GJN-Aerospace/CanSat2020/Ground Station/Hardware/Antenna/Balun.png

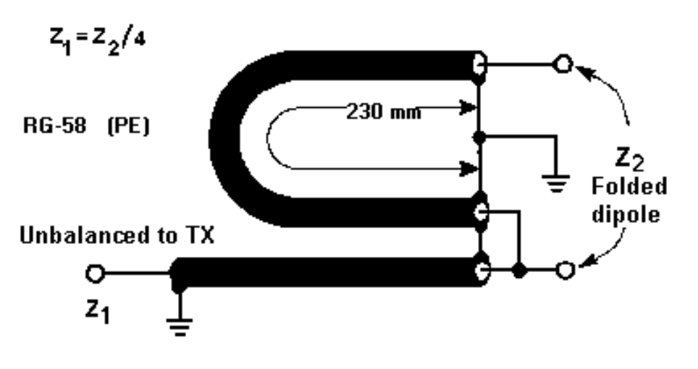
Ground Station/Hardware/Antenna/Balun.png
