GJN-Aerospace/CanSat2020/Probe/Hardware/Components/Battery/Nabíječka Li-ion článku TP4056 s ochranou/LA120013-1.png

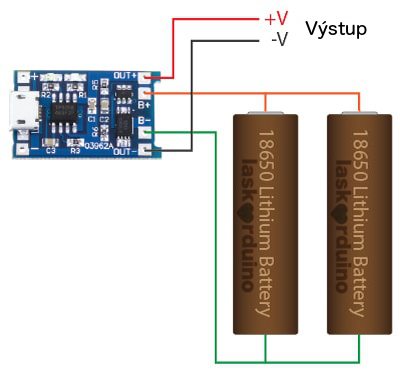
Probe/Hardware/Components/Battery/Nabíječka Li-ion článku TP4056 s ochranou/LA120013-1.png
