GJN-Aerospace/CanSat2020/Probe/Hardware/Components/Battery/Nabíječka Li-ion článku TP4056 s ochranou/TP4056_Protected_Battery_Charger-3.png

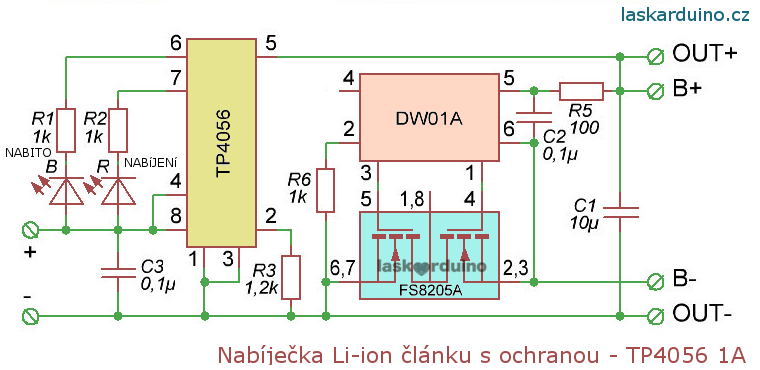
Probe/Hardware/Components/Battery/Nabíječka Li-ion článku TP4056 s ochranou/TP4056_Protected_Battery_Charger-3.png
