GJN-Aerospace/CanSat2020/Probe/Hardware/Components/BME280/Screenshot 2020-01-01 at 14.22.14.png

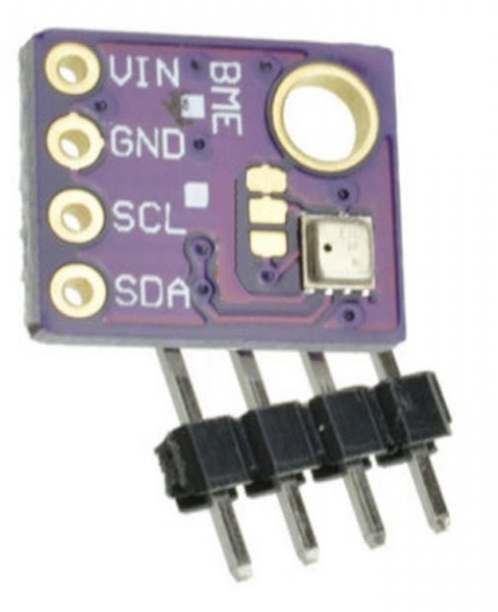
Probe/Hardware/Components/BME280/Screenshot 2020-01-01 at 14.22.14.png
