GJN-Aerospace/CanSat2020/Probe/Hardware/Components/Development board Ncleo F411RE/mbed.com/nucleo_f411re_2017_11_14_ard_left.png

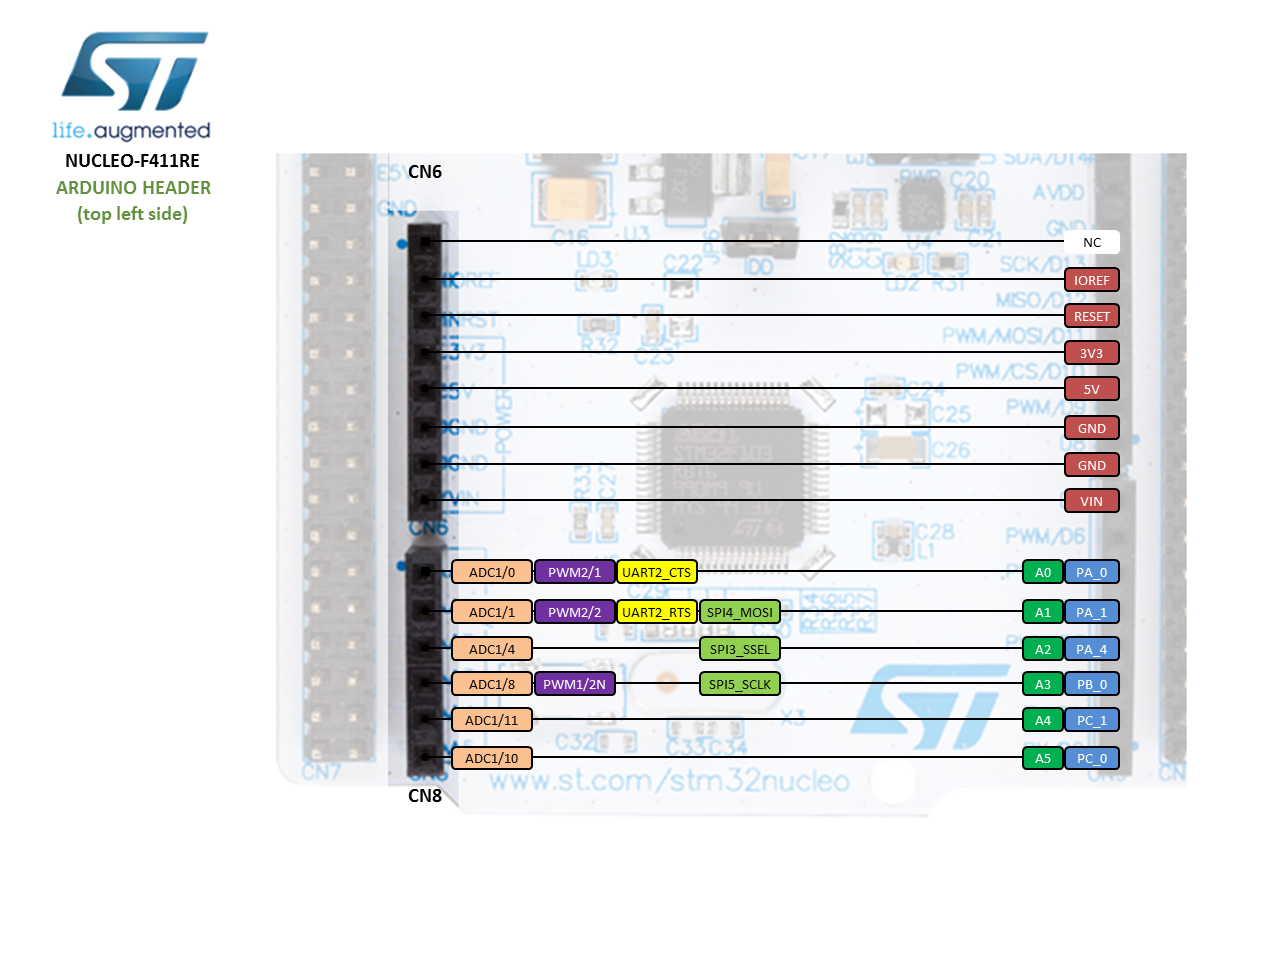
Probe/Hardware/Components/Development board Ncleo F411RE/mbed.com/nucleo_f411re_2017_11_14_ard_left.png
