GJN-Aerospace/CanSat2020/Probe/Hardware/Components/MicroSD Slot/GCT/Screenshot 2019-11-09 at 16.13.04.png

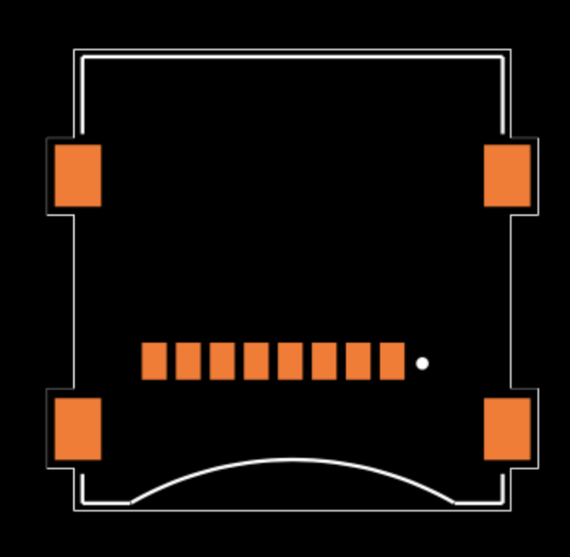
Probe/Hardware/Components/MicroSD Slot/GCT/Screenshot 2019-11-09 at 16.13.04.png
