GJN-Aerospace/CanSat2020/Probe/Hardware/Components/MPU-9250/Screenshot 2020-01-01 at 14.21.57.png

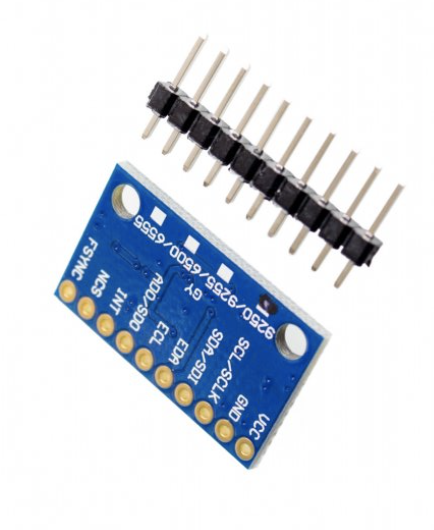
Probe/Hardware/Components/MPU-9250/Screenshot 2020-01-01 at 14.21.57.png
