GJN-Aerospace/CanSat2020/Probe/Hardware/Components/Programmer/STLink/Screenshot 2020-03-07 at 09.58.13.png

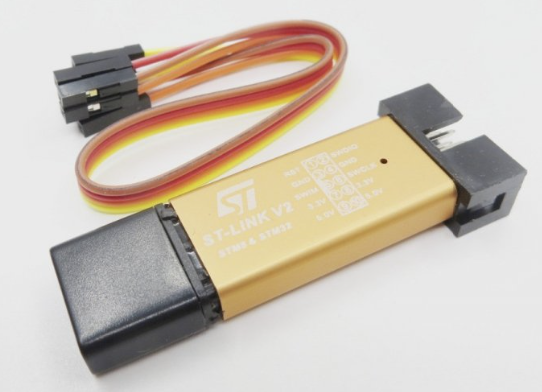
Probe/Hardware/Components/Programmer/STLink/Screenshot 2020-03-07 at 09.58.13.png
