GJN-Aerospace/CanSat2020/Probe/Hardware/Components/Programmer/UART/Screenshot 2020-03-07 at 09.57.16.png

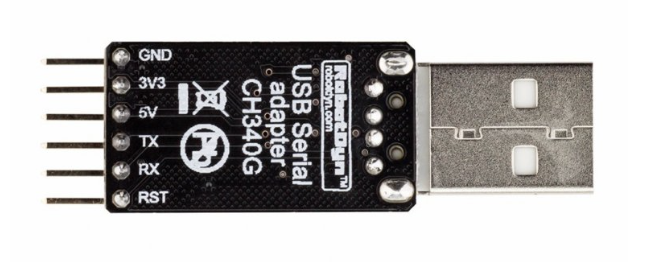
Probe/Hardware/Components/Programmer/UART/Screenshot 2020-03-07 at 09.57.16.png
