GJN-Aerospace/CanSat2020/Probe/openCanSat PKII/PouzdroOCS(PETG).stl

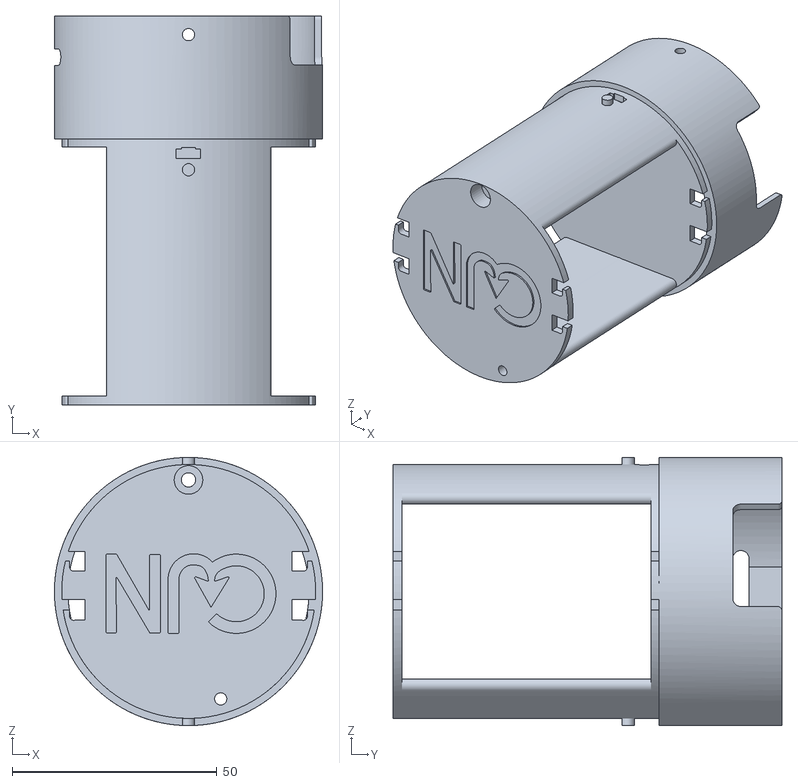
[picture p37: CAD file, 2020-08-19]
Probe/openCanSat PKII/PouzdroOCS(PETG).stl
65.5 x 95.0 x 65.5
