GJN-Aerospace/CanSat2020/Parachute/ParachuteRetainer.stl

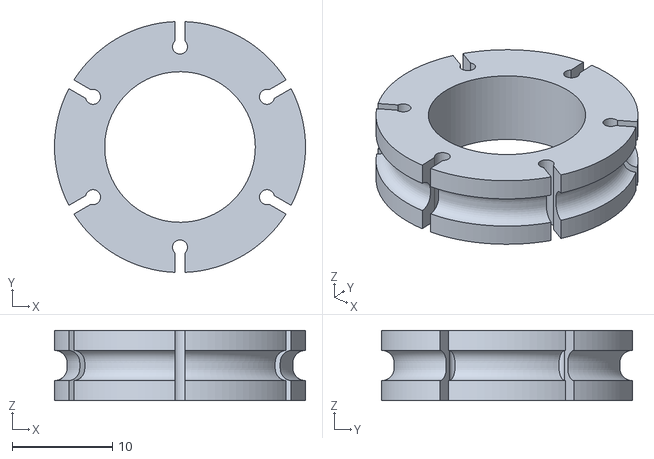
[picture p38: CAD file, 2020-08-19]
Parachute/ParachuteRetainer.stl
25.0 x 25.0 x 7.00
