GJN-Aerospace/CanSat2020/Probe/Hardware/Case/PlastPKII(TPU).stl

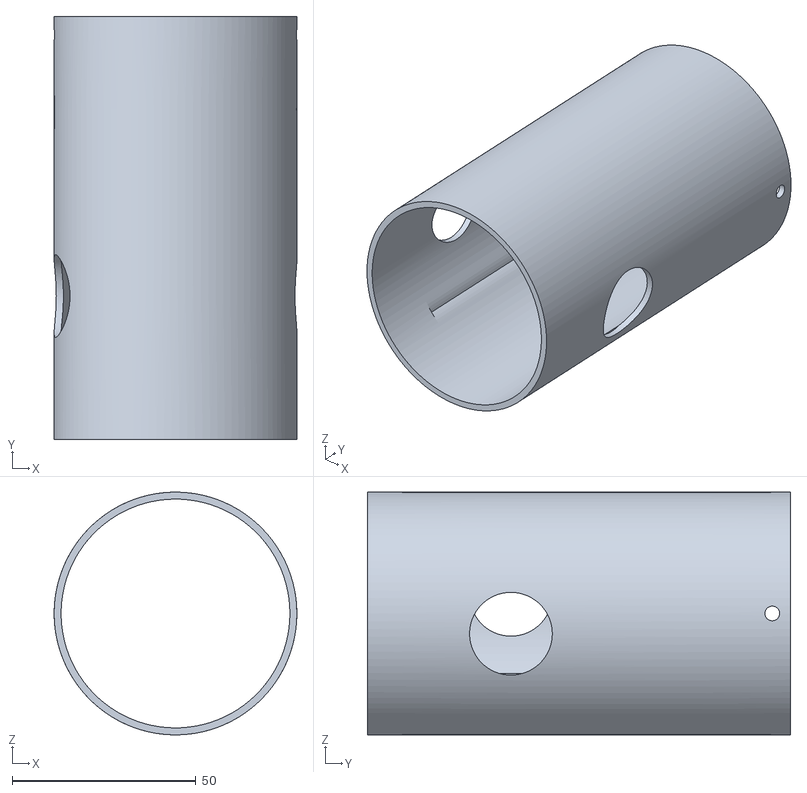
[picture p39: CAD file, 2020-08-19]
Probe/Hardware/Case/PlastPKII(TPU).stl
66.0 x 115.0 x 66.0
