GJN-Aerospace/CanSat2020/Parachute/Kolicek(6x, CPE, co nejdetailnejsi).stl

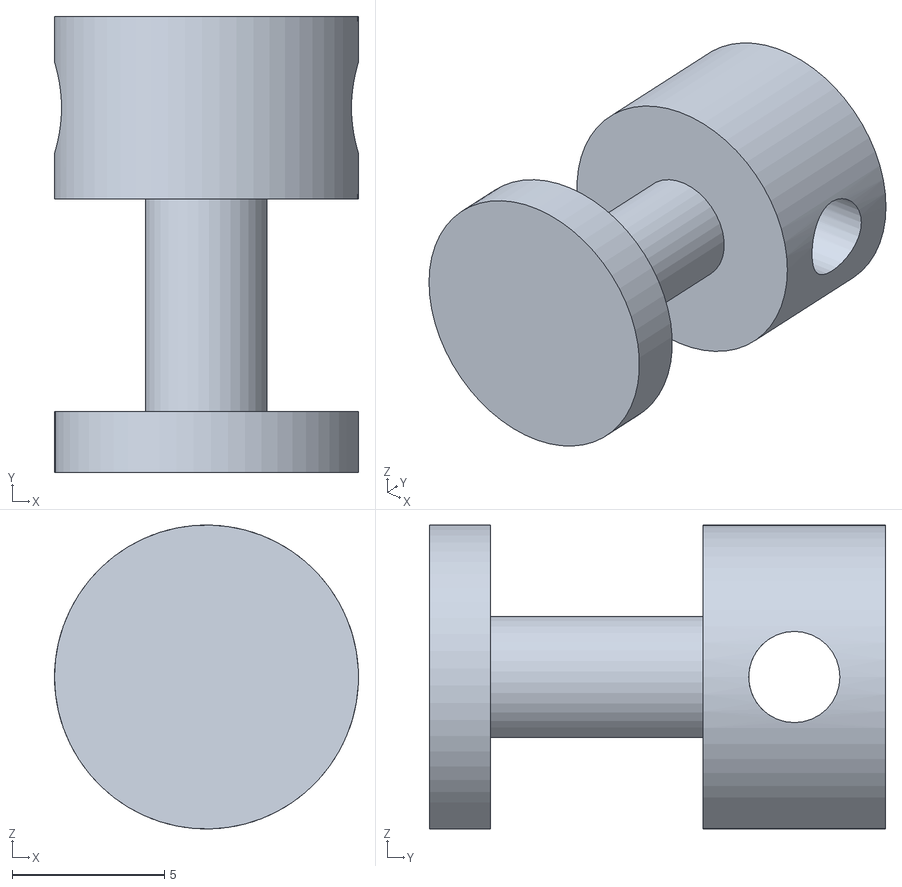
[picture p40: CAD file, 2020-08-19]
Parachute/Kolicek(6x, CPE, co nejdetailnejsi).stl
10.0 x 15.0 x 10.00
