GJN-Aerospace/CanSat2020/Probe/Hardware/Components/Connectors/Battery Connectors/PFH02-03P/dsh.800-085.1.pdf

2510型连接器承认图面 | E

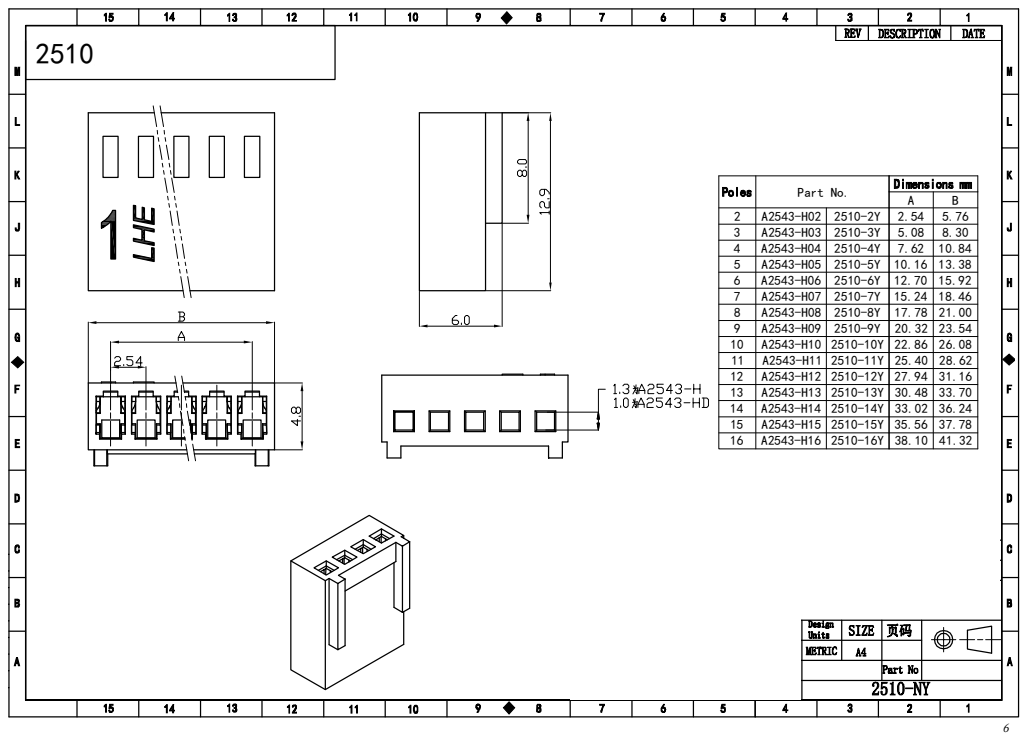
[picture p42: page 1]
PA66(UL94V-0) Housing; White（白色）; 浙江联和电子有限公司 ®; Part No.

27.94 31.16
30.48 33.70
33.02 36.24

ZHEJIANG LIANHE ELECTRONICS CO.,LTD
