GJN-Aerospace/CanSat2020/Probe/Hardware/Components/MicroSD Slot/dsh.832-271.1.pdf

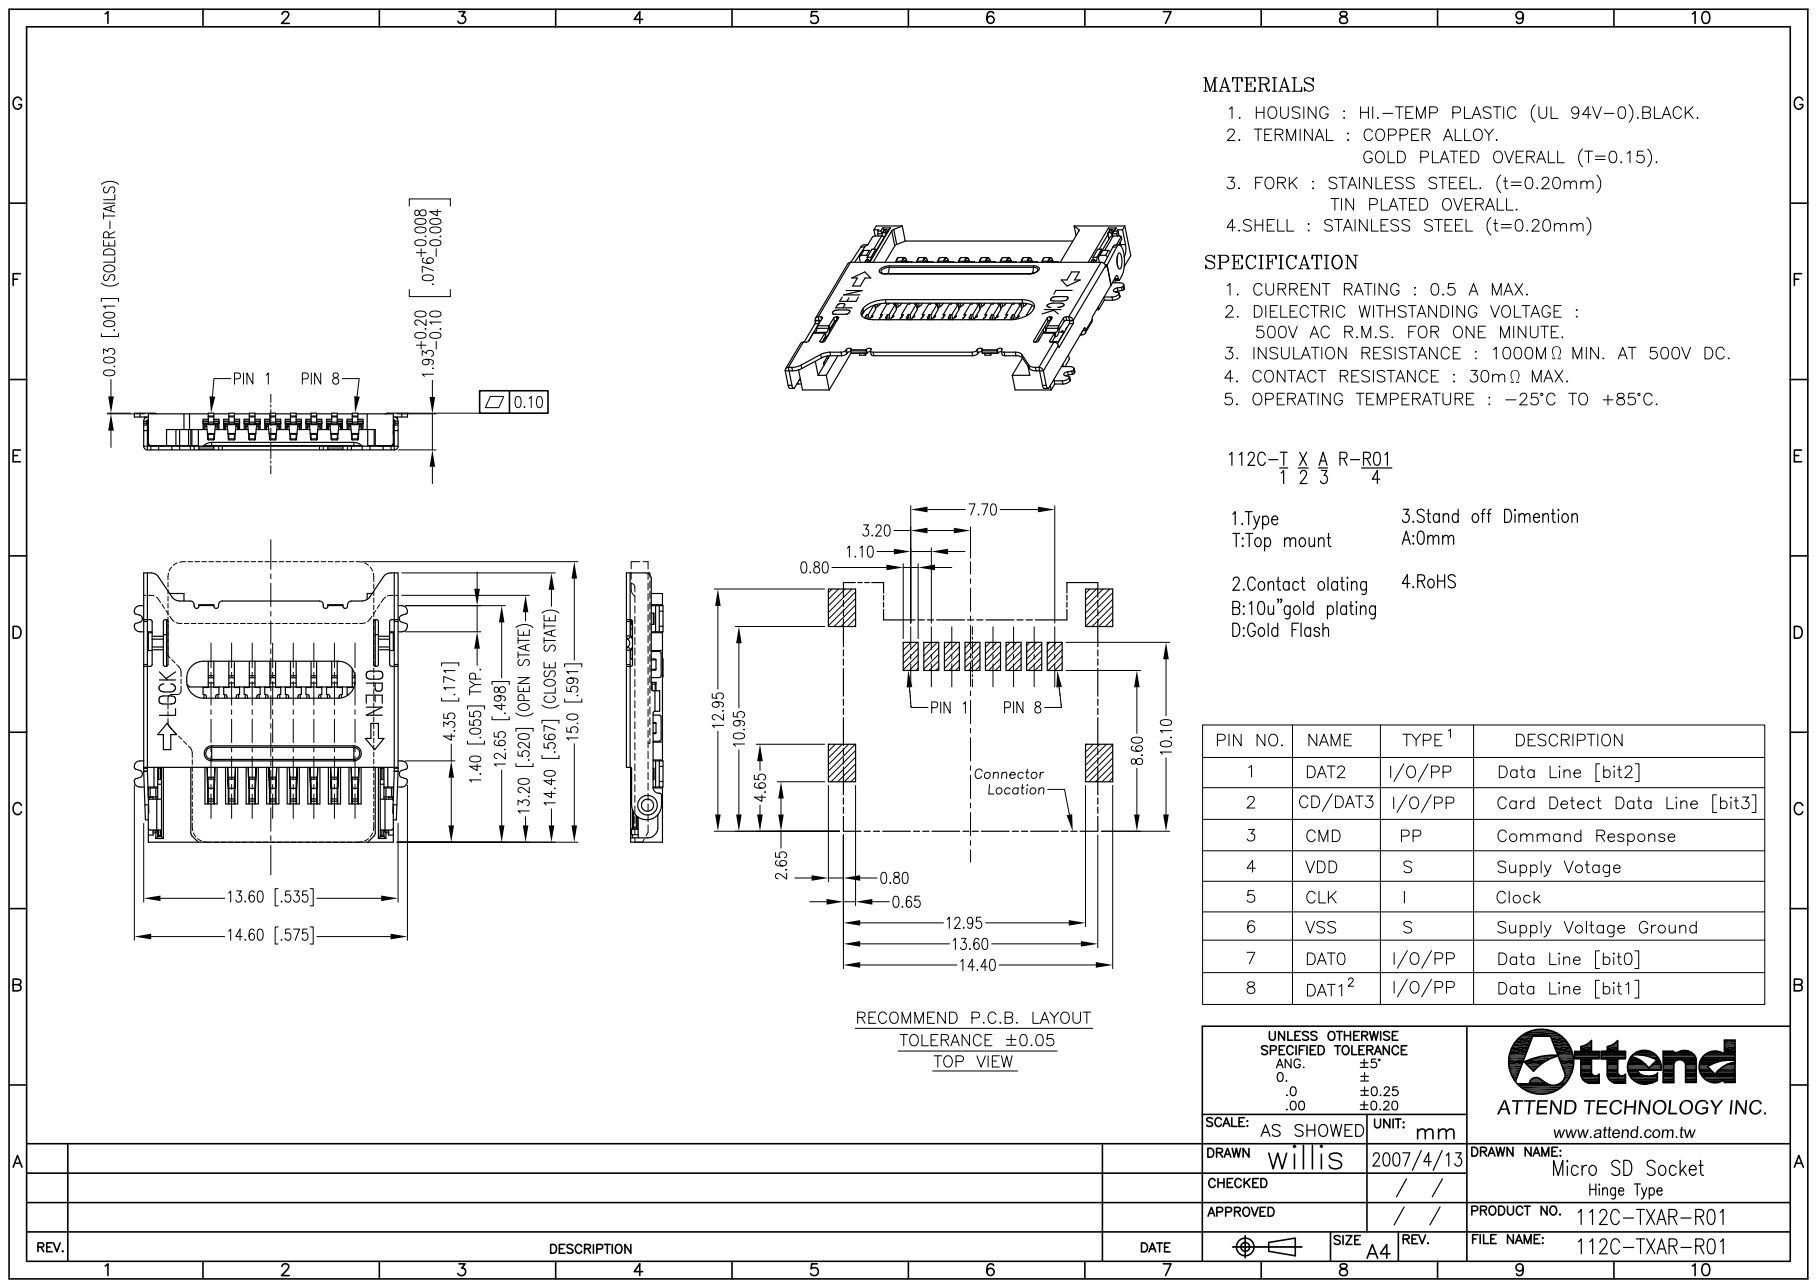
[picture p52: page 1]
